Lawenda700/InkTime/Images/Screenshot (205).png

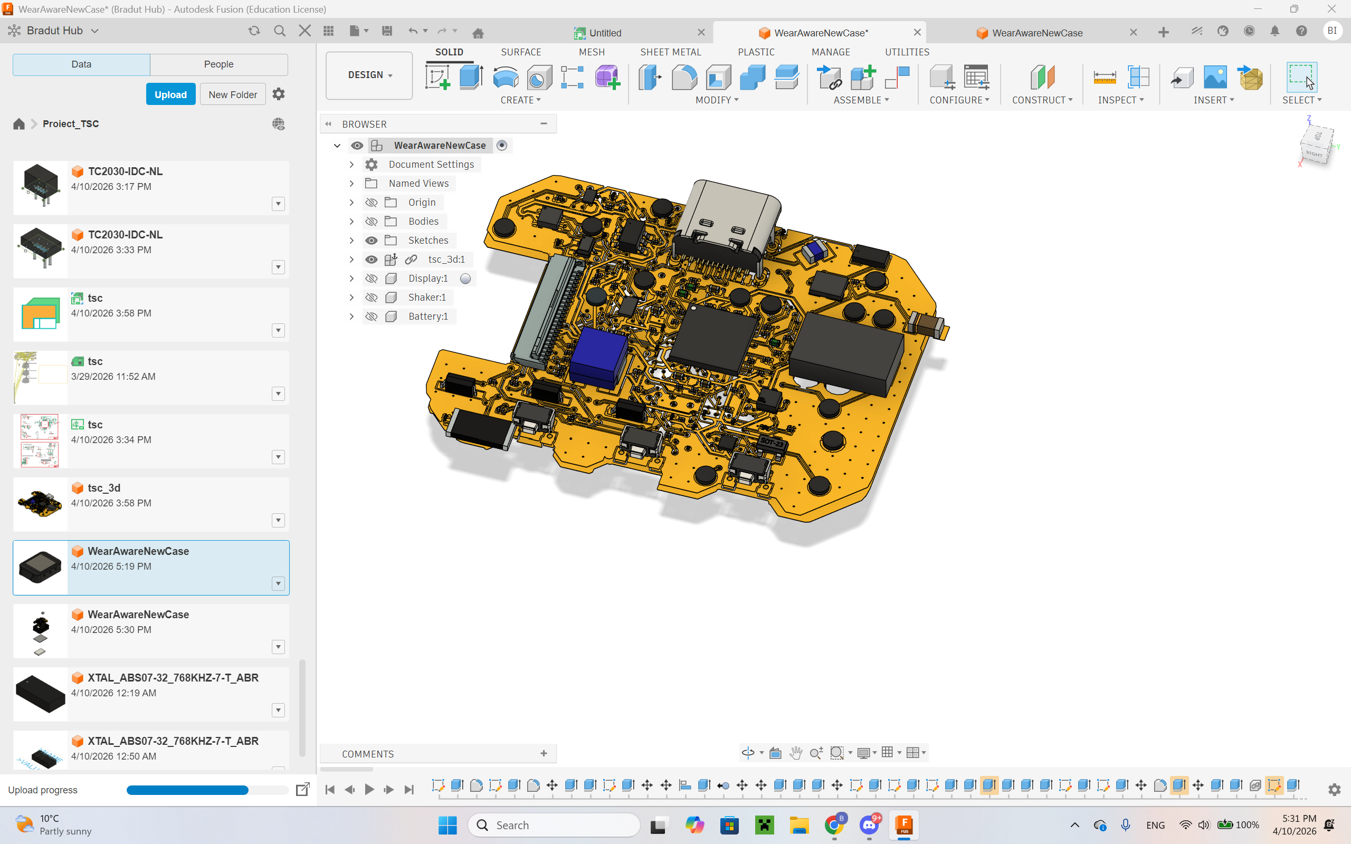
Images/Screenshot (205).png
