Lawenda700/InkTime/Images/Screenshot (207).png

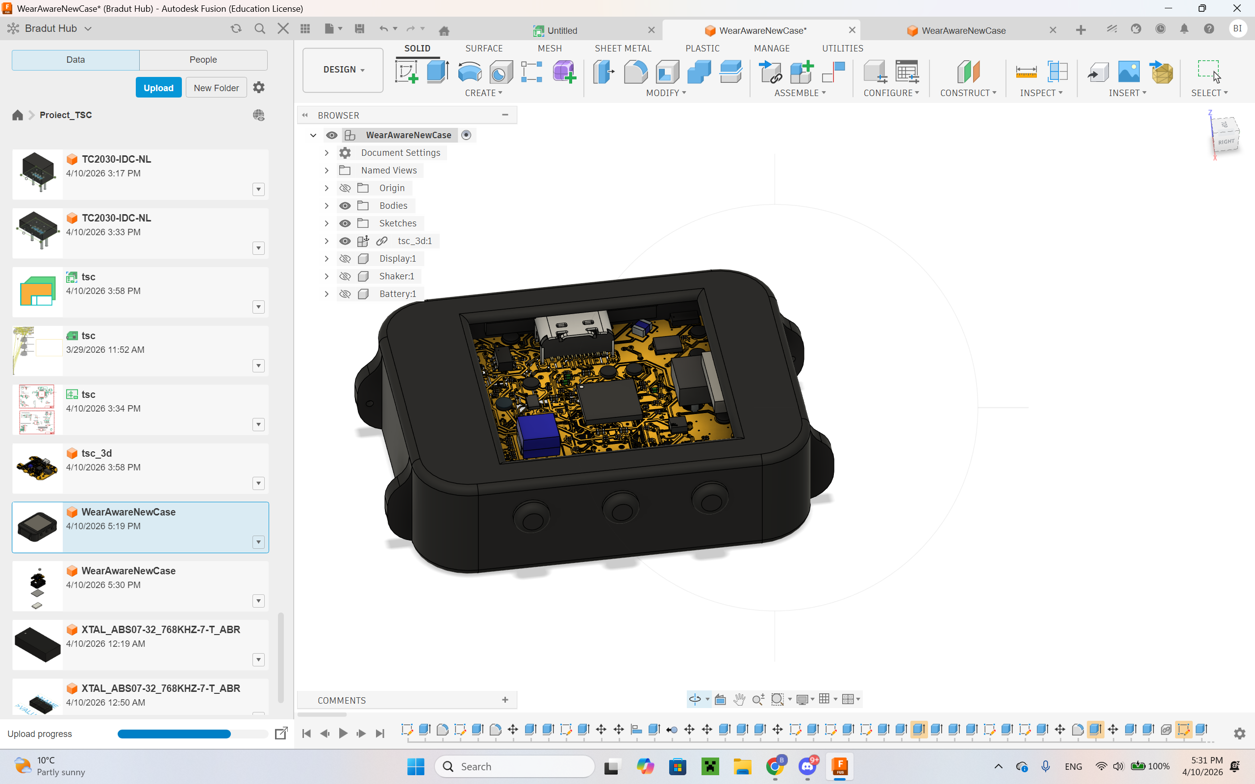
Images/Screenshot (207).png
