Lawenda700/InkTime/Images/Screenshot (209).png

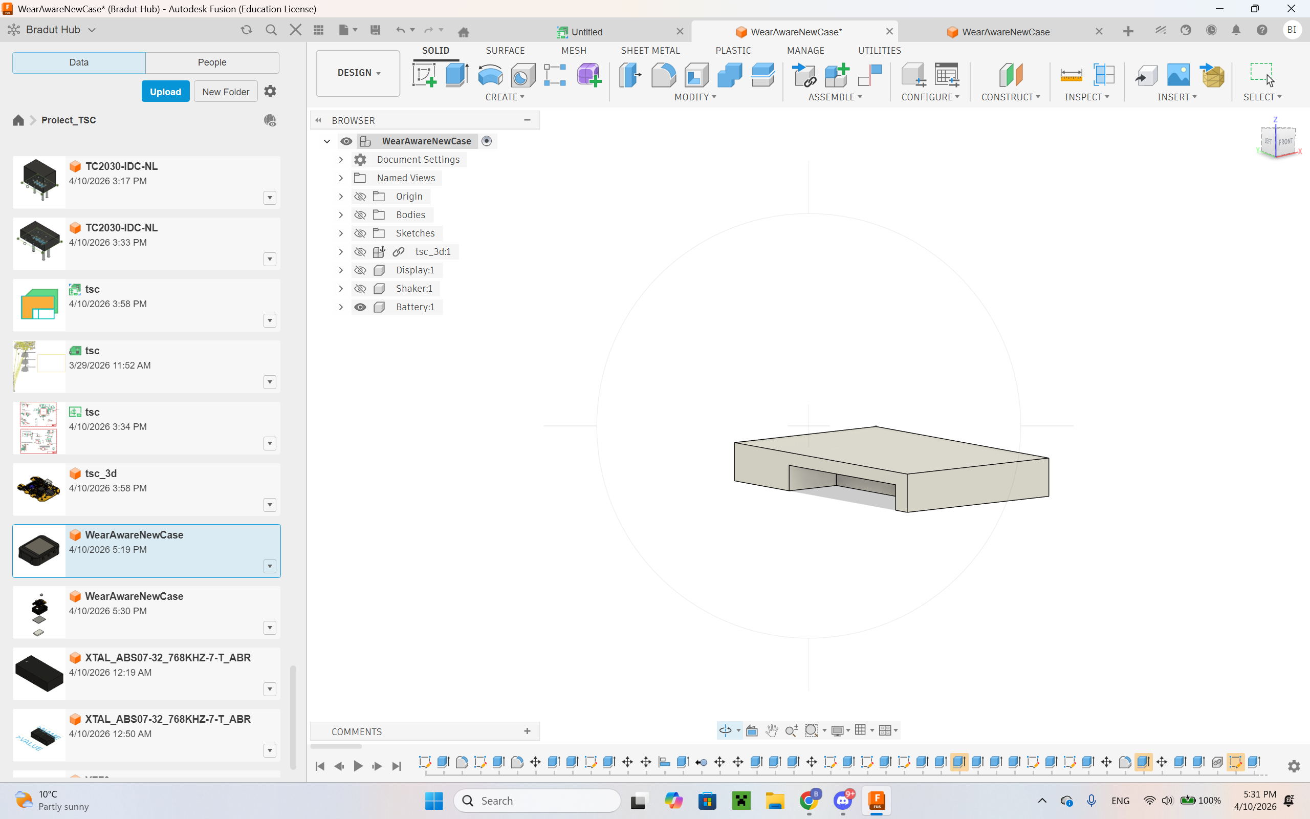
Images/Screenshot (209).png
