Lawenda700/InkTime/Images/Screenshot (212).png

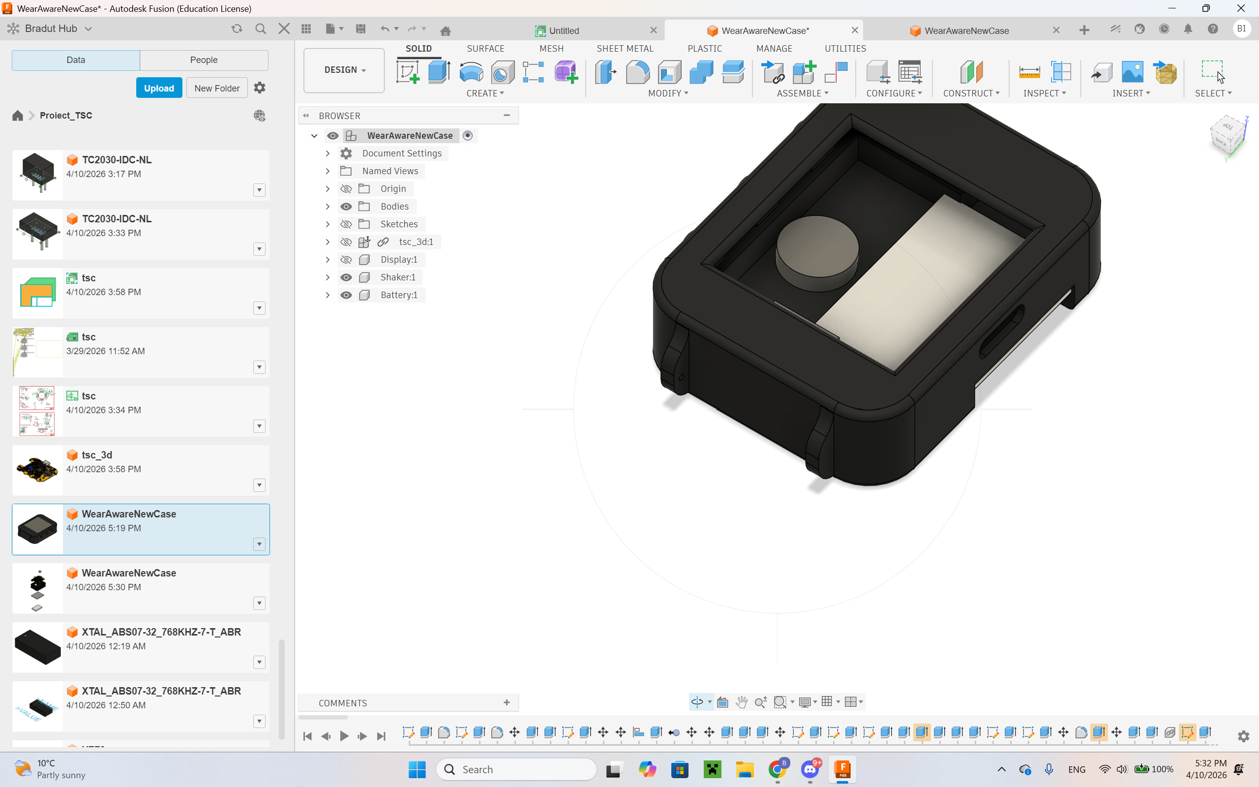
Images/Screenshot (212).png
