Lawenda700/InkTime/Images/Screenshot (216).png

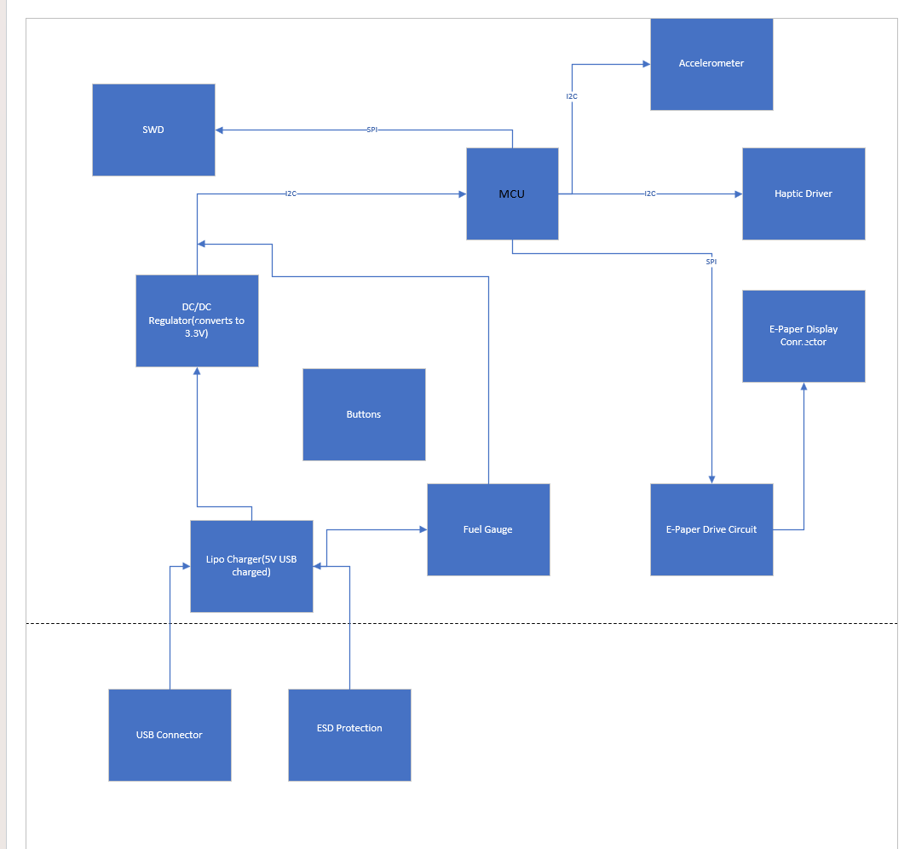
Images/Screenshot (216).png
